kairosbrightside/sensor-box/images/externalpowee.jpg

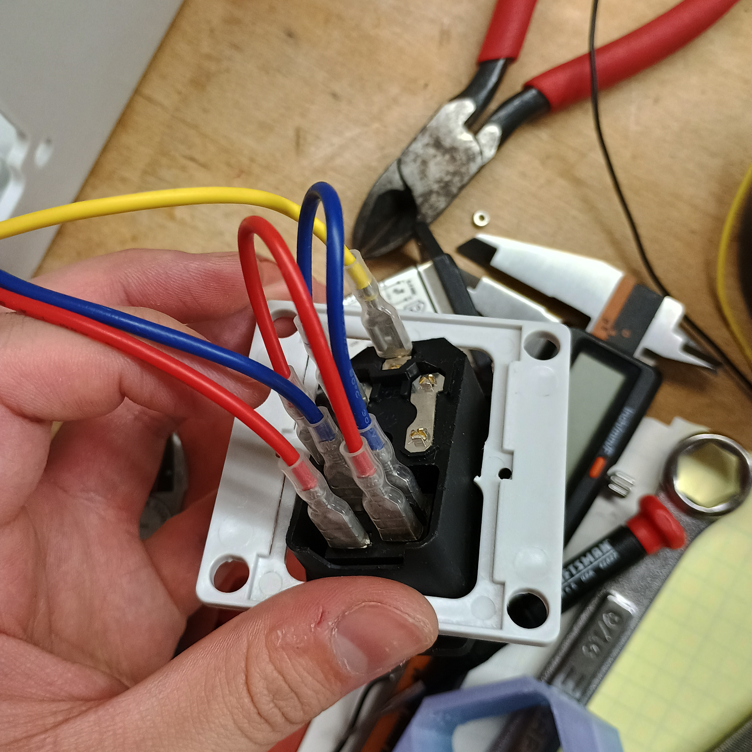
images/externalpowee.jpg
