kairosbrightside/sensor-box/images/filter.jpg

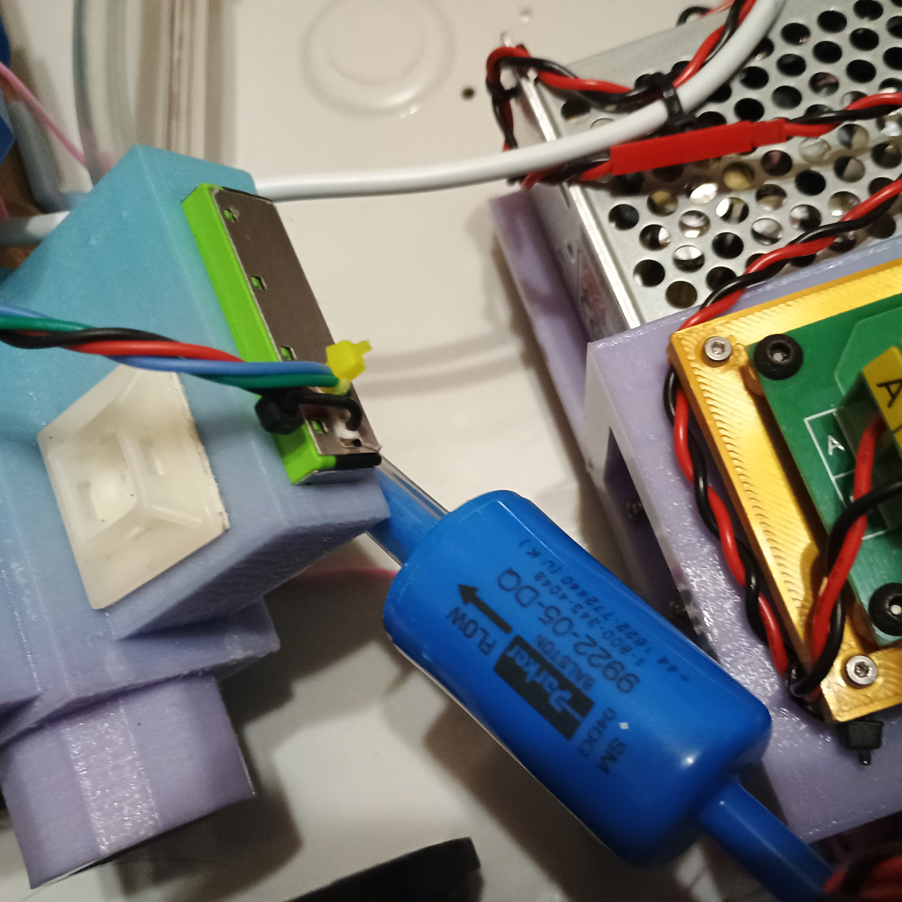
images/filter.jpg
