kairosbrightside/sensor-box/images/heatercontroller.jpg

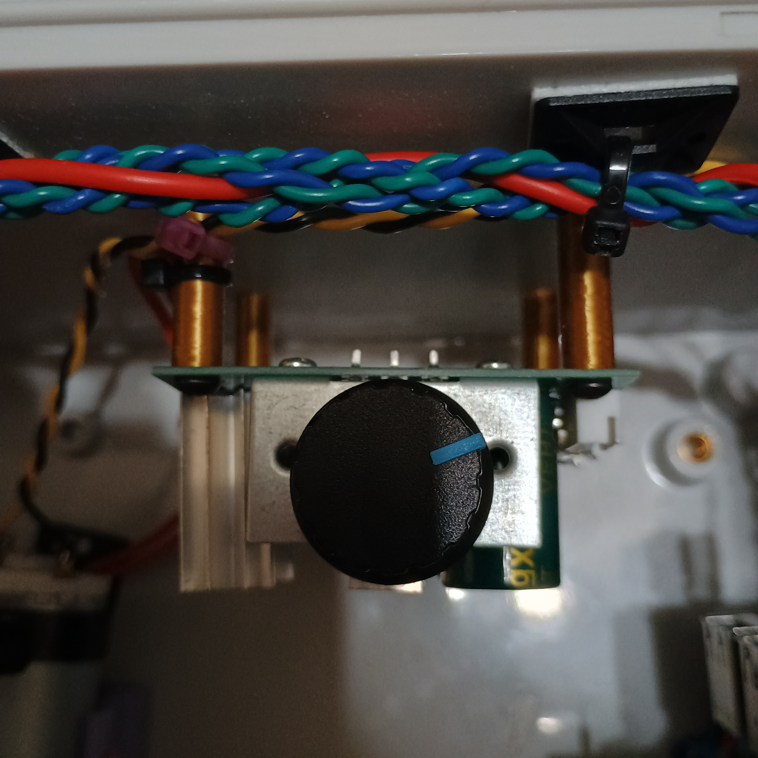
images/heatercontroller.jpg
