kairosbrightside/sensor-box/images/shieldandpipe.jpg

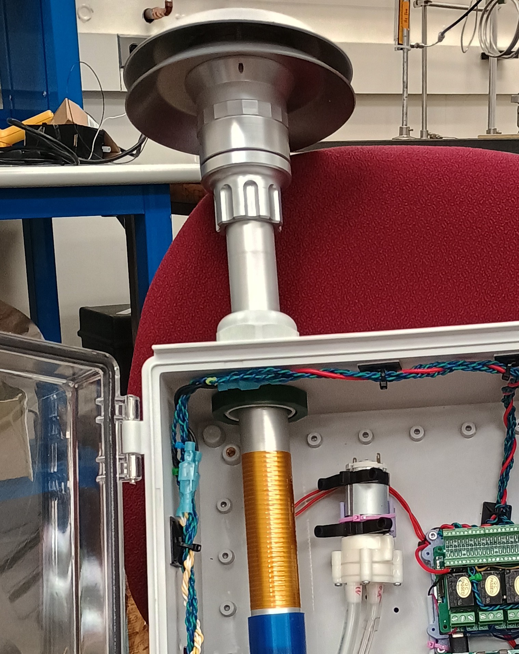
images/shieldandpipe.jpg
